prydin/opamp-frontend-class-ab/spice/opamp-classabs.asc

C1: cap; 22p
C4: cap; 2.2µ
C5: cap; 220p
C6: cap; 1e-20
C7: cap; 220µ
C8: cap; 100µ
C9: cap; 1n
C10: cap; 100n
C11: cap; 1n
C12: cap; 100µ
C13: cap; 100µ
C14: cap; 1µ
C15: cap; 10µ
C16: cap; 100µ
D1: diode; 1N4148
D2: diode; 1N4148
D3: diode; 1N4148
D4: diode; 1N4148
D5: zener; BZX84C15L
D6: diode; 1N4148
D7: diode; 1N4148
D8: diode; 1N4148
D9: diode; 1N4148
D10: zener; BZX84C15L
D11: diode; 1N4148
D13: diode; 1N4148
D14: diode; 1N4007
D15: diode; 1N4148
D16: diode; 1N4148
D17: diode; 1N4007
L1: ind; 1µ
Q1: pnp; BD140C
Q2: pnp; 2N5401
Q3: npn; 2N5550
Q4: pnp; 2N5401
Q5: npn; 2N5550
Q6: pnp; 2N5401
Q7: npn; BD139C
Q8: npn; 2N5550
Q9: npn; MJL3281C
Q10: npn; BD139C
Q11: npn; BD139C
Q12: pnp; BD140C
Q13: pnp; MJL1302C
R1: res; 33k
R2: res; 10
R3: res; 510
R4: res; 330
R5: res; 10k
R6: res; 820
R7: res; 330
R8: res; 10k
R9: res; 820
R10: res; 100
R11: res; 1k
R12: res; 33k
R13: res; 1k
R14: res; 10
R15: res; 510
R16: res; 100
R17: res; 33
R18: res; 0.33
R19: res; 1k
R20: res; 10
R21: res; 10
R22: res; 33
R23: res; 1k
R24: res; 100
R25: res; 100
R26: res; 8
R27: res; 2.7k
R28: res; 0.33
R29: res; 470
RV1: res; 1k
U1: NE5532
V1: voltage; 28; Rser=0.1
V2: voltage; 28; Rser=0.1
V3: voltage; SINE(0 0.5 1k) AC 0
V6: voltage; AC 1
Named nets: 0, VCC, VEE, X, Y, op
.ac dec 100 1 1e7
.tran 0 100m 0 1u
.option plotwinsize=0 NoOpiter numdgt=15
.four 1k 50 -1 v(x)
